alexcwu1121/hammerhead-turret-controller/htc/bsp.cpp

#include "bsp.hpp"

#include "tim.h"

/// @brief Flag tracking pan low state
static volatile bool pan_step_low = false;
/// @brief Flag tracking tilt low state
static volatile bool tilt_step_low = false;

// Interrupt callbacks
extern "C"
{
void SysTick_Handler(void)
{
    // Increment hal counter
    HAL_IncTick();
}

void TIM4_IRQHandler(void)
{
    HAL_TIM_IRQHandler(&htim4);
}

//void TIM6_IRQHandler(void)
//{
//    HAL_TIM_IRQHandler(&htim4);
//}

// __HAL_TIM_SET_AUTORELOAD(&htim4, new_period);
void HAL_TIM_PeriodElapsedCallback(TIM_HandleTypeDef *htim)
{
    if (htim->Instance == TIM4)
    {
        //HAL_GPIO_WritePin(PAN_STEP_GPIO_Port, PAN_STEP_Pin, GPIO_PIN_SET);
        //__NOP(); __NOP(); __NOP();  // small delay (~100 ns each)
        //HAL_GPIO_WritePin(PAN_STEP_GPIO_Port, PAN_STEP_Pin, GPIO_PIN_RESET);
        HAL_GPIO_WritePin(TILT_STEP_GPIO_Port, TILT_STEP_Pin, GPIO_PIN_RESET);
        HAL_GPIO_WritePin(PAN_STEP_GPIO_Port, PAN_STEP_Pin, GPIO_PIN_RESET);
        __NOP();
        __NOP();
        __NOP();  // small delay (~100 ns each)
        HAL_GPIO_WritePin(TILT_STEP_GPIO_Port, TILT_STEP_Pin, GPIO_PIN_SET);
        HAL_GPIO_WritePin(PAN_STEP_GPIO_Port, PAN_STEP_Pin, GPIO_PIN_SET);
    }
}

// __HAL_TIM_SET_AUTORELOAD(&htim6, new_period);
void TIM6_DAC_IRQHandler(void)
{
    /*
    if (LL_TIM_IsActiveFlag_UPDATE(TIM6))
    {
        LL_TIM_ClearFlag_UPDATE(TIM6);

        HAL_GPIO_WritePin(TILT_STEP_GPIO_Port, TILT_STEP_Pin, GPIO_PIN_SET);
        __NOP(); __NOP(); __NOP();  // small delay (~100 ns each)
        HAL_GPIO_WritePin(TILT_STEP_GPIO_Port, TILT_STEP_Pin, GPIO_PIN_RESET);
    }
    */
}
}

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
